openSX70/openSX70-PCB/CURRENT/openSX70_LENS&BELLOWS_V5.1-SEEED_20180224-blue.png

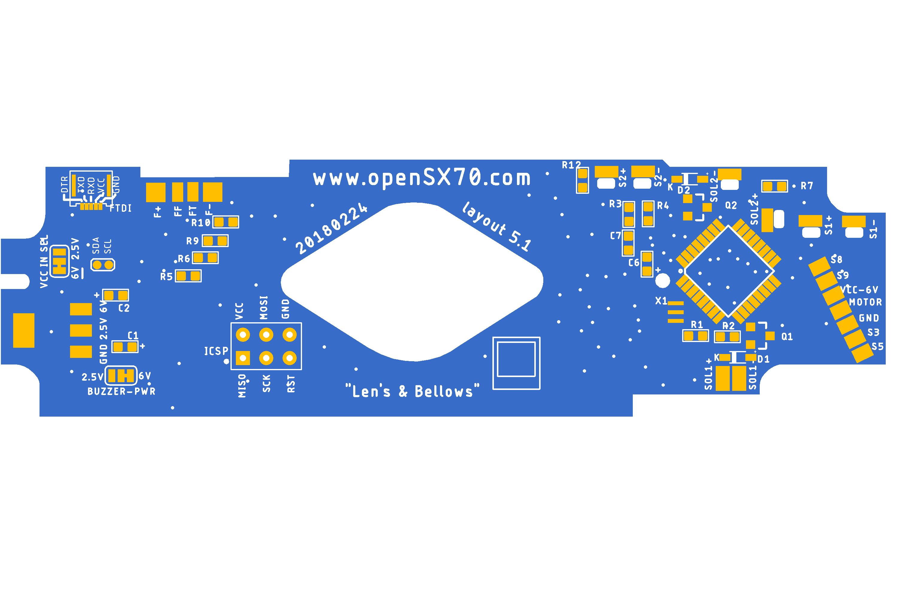
CURRENT/openSX70_LENS&BELLOWS_V5.1-SEEED_20180224-blue.png
