openSX70/openSX70-PCB/CURRENT/sonar-FBW/openSX70_SONAR_8-9-3-8-S4-TCS3200-202000606.xlsx

Sheet: openSX70-sonar-PCBWAY BOM
 |  |  | BOM
Item # | *Ref Des | *Qty | Manufacturer | *Mfg Part # | Description / Value | *Package | Type | Your Instructions / Notes
1 | C1, C4 | 2 | any/open AVL | 10uF | CERAMIC-10UF-10V-10%-X5R(0603) | C0603 | SMD | any brand-name manufacturer from AVL
2 | C2, C3, C5, C6, C7, C8, C9 | 7 | any/open AVL | 100nF | CERAMIC-100NF-50V-10%-X7R(0603) | C0603 | SMD | any brand-name manufacturer from AVL
3 | R2, R4, R16 | 3 | any/open AVL | 100K | SMD-RES-100K-5%-1/10W(0603) | R0603 | SMD | any brand-name manufacturer from AVL
4 | R1, R3, R7, R23 | 4 | any/open AVL | 100R | SMD-RES-100R-5%-1/10W(0603) | R0603 | SMD | any brand-name manufacturer from AVL
5 | R5, R8, R12, R14, R9, R24 | 6 | any/open AVL | 10K | SMD-RES-10K-1%-1/10W(0603) | R0603 | SMD | any brand-name manufacturer from AVL
6 | R6, R10, R13, R15, R25 | 6 | any/open AVL | 12K | SMD-RES-12K-1%-1/10W(0603) | R0603 | SMD | any brand-name manufacturer from AVL
7 | R11, R18, R20, R22 | 4 | any/open AVL | 1K 1/10W | SMD-RES-1K-5%-1/10W(0603) | R0603 | SMD | any brand-name manufacturer from AVL
8 | R19 | 1 | any/open AVL | 150R 1/10W | SMD-RES-150R-5%-1/10W(0603) | R0603 | SMD | any brand-name manufacturer from AVL
9 | R21 | 1 | any/open AVL | 180R 1/10W | SMD-RES-180R-5%-1/10W(0603) | R0603 | SMD | any brand-name manufacturer from AVL
10 | R17 | 1 | any/open AVL | 120K 1/10W | SMD-RES-120K-5%-1/10W(0603) | R0603 | SMD | any brand-name manufacturer from AVL
11 | D1, D2 | 2 | any/open AVL | 1N4148WS | 1N4148WS Series 75 V 300 mA Surface Mount Small Signal Diodes | SOD323 | SMD | Polarity marked
12 | Q1, Q2 | 2 | Alpha Omega | MOSFET-NCH-AO3404A | 5.8A/30V/35mΩ | SOT23-3 | SMD | DO NOT REPLACE MUST USE THIS
13 | J1 | 1 | Wurth Electronics | 687106183722 | WR-FPC SMT Horiztl .50mm Bott Cont 6P | 687106183722 | SMD
14 | U1 | 1 | Microchip Technology | ATMEGA328P-MU | ATMEGA328P_32MLF | MLF32 | SMD | no thermal pad implemented there are NO vias under
15 | U2 | 1 | Texas Instruments | TPS79533DCQR | Ultralow-Noise, High-PSRR, Fast, RF, 500-mA Low-Dropout Linear Regulators 6-SOT-223 -40 to 125 | SOT-223-6 | SMD | 3.3V operation
16 | X1 | 1 | Murata Electronics North America | CSTNE8M00G550000R0 | Resonators 8.0000MHz 33pF SMD | CFP95P160X100-3N | SMD | Resonators 8MHz 5%
17 | LED | 1 | Lite-On Inc. | LTST-C195TBJRKT | Blue/Red Clear | 0606 | SMD
18 | U3 | 1 | AMS | TCS3200D-TR | Light To Frequency & Light To Voltage Light to Frequency High Responsivity | SOIC8 | SMD
19 | Q3 |  | any/open AVL | BC8743 | NPN transistor | SOT-23 | SMD
20 | Q4 |  | Diodes Incorporated | DMP2035U-7 | MOSFET MOSFET P-CHANNEL | SOT-23 | SMD
 |  | 45
 |  |  | AVL (Approved Vendor List)
 |  |  | TDK, Murata, Taiyo Yuden, AVX, Panasonic, Samsung, Vishay, ON Semiconductor, Diodes Incorporated

Sheet: openSX70_SONAR_8-8-S4-TCS3200-2
item# | ref desp | Qty | manufacturer | Value | Device | Package | type | Description
1 | C1, C4 | 2 | various | 10uF | CERAMIC-10UF-10V-10%-X5R(0603) | C0603 | SMD | 302010103
2 | C2, C3, C5, C6, C7, C8, C9 | 7 | various | 100nF | CERAMIC-100NF-50V-10%-X7R(0603) | C0603 | SMD | 302010138
3 | R2, R4 | 2 | various | 100K | SMD-RES-100K-5%-1/10W(0603) | R0603 | SMD | 301010089
4 | R1, R3, R7 | 3 | various | 100R | SMD-RES-100R-5%-1/10W(0603) | R0603 | SMD | 301010090
5 | R8, R12, R14, R16, R5, R9 | 6 | various | 10K | SMD-RES-10K-1%-1/10W(0603) | R0603 | SMD | 301010299
6 | R6, R10, R13, R15, R17 | 5 | various | 12K | SMD-RES-12K-1%-1/10W(0603) | R0603 | SMD | 301010299
7 | R11, R18 | 2 | various | 1K 1/10W | SMD-RES-1K-5%-1/10W(0603) | R0603 | SMD | 301010291
8 | D1, D2 | 2 | various | 1N4148WS | Small Signal Fast Switching Diode | SOD323 | SMD | 1N4148WS Series 75 V 300 mA Surface Mount Small Signal Diodes - SOD-323F
9 | Q1, Q2 | 2 | Alpha Omega | 5.8A/30V/35mΩ | MOSFET-NCH-AO3404A | SOT23-3 | SMD | N-channel MOSFETs
10 | J1 | 1 | Wurth Electronics | 687106183722 | WR-FPC SMT Horiztl .50mm Bott Cont 6P | 687106183722 | SMD
11 | U1 | 1 | ATMEL | ATMEGA328P_32MLF | ATMEGA328P_32MLFATMEGA328-MLF | MLF32 | SMD
12 | U2 | 1 | Texas Instruments | TPS79533DCQR | TPS79501DCQ | SOT-223-6 | SMD | Ultralow-Noise, High-PSRR, Fast, RF, 500-mA Low-Dropout Linear Regulators 6-SOT-223 -40 to 125
13 | Y1 | 1 | MURATA | CSTCE8M00G52Z-R0 | CER RES 16.0000MHZ 15PF SMD | CFP95P160X100-3N | SMD | Ceramic Resonator 16MHz ±0.5% (Tol) ±0.3% (Stability) 15pF 40Ohm 3-Pin CSMD T/R
14 | LED | 1 | Lite-On Inc. | LTST-C195KGJRKT | BI-LED RED GREEN | 0606 | SMD
15 | TCS3200 | 1 | TAOS | TCS3200D | TCS3200D | SOIC8 | SMD

Sheet: PCBWAY example
 |  |  | BOM
Item # | *Ref Des | *Qty | Manufacturer | *Mfg Part # | Description / Value | *Package | Type | Your Instructions / Notes
1 | U2 | 1 | STMicroelectronics | LIS3MDLTR | SENSOR MAGMTR I2C/SPI 12LGA | 12LGA | SMD | Align dot on chip with dot on PCB (pin 1)
2 | U1 | 1 | STMicroelectronics | LSM6DS33TR | IMU ACCEL/GYRO I2C/SPI 16LGA | 16LGA | SMD | Align dot on chip with dot on PCB (pin 1)
3 | C1,C2,C3,C4 | 4 | Yageo | CC0603KRX7R7BB104 | CAP CER 0.1UF 16V X7R 0603 | 0603 | SMD
4 | C5 | 1 | Murata Electronics North America | GRM188R61C105MA12D | CAP CER 1UF 16V X5R 0603 | 0603 | SMD
5 | J1 | 1 | JST Sales America Inc. | SM09B-SRSS-TB(LF)(SN) | CONN HEADER SH 9POS SIDE 1MM TIN | 9POS | SMD
