openSX70/openSX70-PCB/CURRENT/GERBERS/openSX70_LENS&BELLOWS_V5.2-SEEED_20180226_NO_BUZZER.csv

Designator | Manufacturer Part Number | Quantity
LED1 | 17-215UYC/S530-A3/TR8 | 1
C7, C2, C6 | CC0603KRX7R9BB104 | 3
R2, R4 | RC0603FR-07100KL | 2
R1, R3, R7 | RC0603JR-07100RL | 3
R6, R10, R12 | RC0603FR-0710KL | 3
C1, C5 | CC0603KRX5R6BB106 | 2
R5, R9 | RC0603FR-0715KL | 2
R8, R13 | RC0603FR-071KL | 2
D1,D2 | 1N4148WS | 2
R14 | RC0603JR-074K7L | 1
Q1, Q2 | AO3404A | 2
U1 | ATMEGA328P-AU | 1
U3 | BH1750FVI-TR | 1
Y1 | CSTCE8M00G52Z-R0 | 1
J1 | 687106183722 | 1
LD11172.5V | LD1117S25CTR | 1
