openSX70/openSX70-PCB/CURRENT/openSX70_ALPHA_V8-20181105-MLF32.brd

## EAGLE design CURRENT/openSX70_ALPHA_V8-20181105-MLF32.brd (2018-11-05)

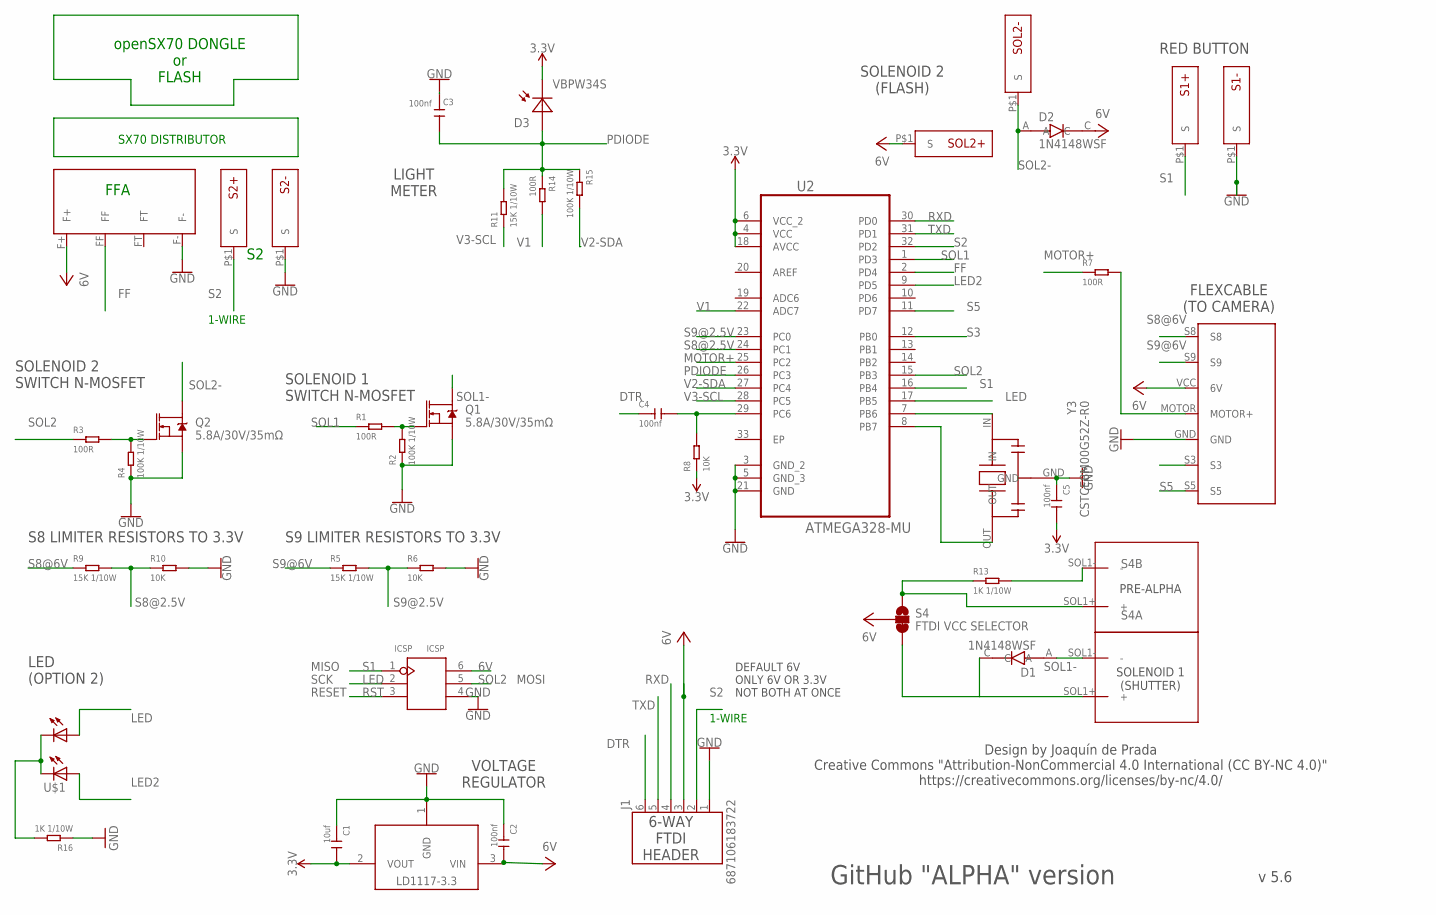
[picture p19: schematic openSX70_ALPHA_V8-20181105-MLF32.sch]

Parts:
C1: 10uf; C0603
C2, C3, C4, C5: 100nf; C0603
D1, D2: 1N4148WSF; SODFL2512X100N
D3: VBPW34S; SOD6439X130N
ICSP: ICSP; H2X3-2.54
J1: 687106183722
LD11172.5V: LD1117 2.5V; SOT223
Q1, Q2: 5.8A/30V/35mΩ; SOT23-3
R1, R3, R7, R14: 100R; R0603
R2, R4, R15: 100K 1/10W; R0603
R5, R9, R11: 15K 1/10W; R0603
R6, R8, R10: 10K; R0603
R13, R16: 1K 1/10W; R0603
S1+, S1-, S2+, S2-: SX70-S-PAD-NEW; SX70-S-PAD2
S4: FTDI VCC SELECTOR; SMT-JUMPER_3_1-NC_TRACE_SILK
SOL1, SOL2: SX70-SOLENOID1-2PADS; SX70-SOLENOID1-2
SOL2+, SOL2-: SX70-S-PAD-NEW; SX70-S-PAD2
U2: ATMEGA328-MU; QFN50P500X500X100-33N
U$1: DUAL-LED-0603-BIS; LED_APHB1608SYKSURKC
U$2: FFA; FFA-PAD-PACKAGE
U$3: SX70-7-PAD; SX70-7-PAD-PROPER
Y3: CSTCE8M00G52Z-R0; CFP95P160X100-3N

Connections:
3.3V: C1.2, C5.2, D3.C, LD11172.5V.2 (VOUT), R8.1, U2.4 (VCC), U2.6 (VCC_2), U2.18 (AVCC)
6V: C2.2, D2.C, ICSP.6 (VCC), J1.3 (4), LD11172.5V.3 (VIN), S4.2, SOL2+.P$1, U$2.F+, U$3.VCC (6V)
DTR: C4.1, J1.6 (1)
FF: U2.2 (PD4), U$2.FF
GND: C1.1, C2.1, C3.2, C5.1, ICSP.4 (GND), J1.1 (6), LD11172.5V.1 (GND), Q1.2 (S), Q2.2 (S), R2.1, R4.1, R6.2, R10.2, R16.1, S1-.P$1, S2-.P$1, U2.3 (GND_2), U2.5 (GND_3), U2.21 (GND), U$2.F-, U$3.GND, Y3.GND
LED: ICSP.2 (SCK), U2.17 (PB5), U$1.1 (A)
LED2: U2.9 (PD5), U$1.3 (A1)
MOTOR+: R7.1, U2.25 (PC2)
MOTOR-HEADER: R7.2, U$3.MOTOR (MOTOR+)
unnamed: Q1.1 (G), R1.2, R2.2
unnamed: D1.C, S4.3, SOL1.SOL1+ (+)
unnamed: Q2.1 (G), R3.2, R4.2
unnamed: U2.7 (PB6), Y3.IN
unnamed: R16.2, U$1.2 (C), U$1.4 (C1)
unnamed: R13.2, SOL2.SOL1- (-)
unnamed: R13.1, S4.1, SOL2.SOL1+ (+)
unnamed: U2.8 (PB7), Y3.OUT
unnamed: C4.2, R8.2, U2.29 (PC6)
PDIODE: C3.1, D3.A, R11.2, R14.1, R15.1, U2.26 (PC3)
RST: ICSP.3 (RST)
RXD: J1.4 (3), U2.30 (PD0)
S1: ICSP.1 (MISO), S1+.P$1, U2.16 (PB4)
S2: J1.2 (5), S2+.P$1, U2.32 (PD2)
S3: U2.12 (PB0), U$3.S3
S5: U2.11 (PD7), U$3.S5
S8@2.5V: R9.2, R10.1, U2.24 (PC1)
S8@6V: R9.1, U$3.S8
S9@2.5V: R5.2, R6.1, U2.23 (PC0)
S9@6V: R5.1, U$3.S9
SOL1: R1.1, U2.1 (PD3)
SOL1-: D1.A, Q1.3 (D), SOL1.SOL1- (-)
SOL2: ICSP.5 (MOSI), R3.1, U2.15 (PB3)
SOL2-: D2.A, Q2.3 (D), SOL2-.P$1
TXD: J1.5 (2), U2.31 (PD1)
V1: R14.2, U2.22 (ADC7)
V2-SDA: R15.2, U2.27 (PC4)
V3-SCL: R11.1, U2.28 (PC5)

Notes on the sheet:
1-WIRE
FFA
LIGHT METER
FLEXCABLE (TO CAMERA)
RED BUTTON
SOLENOID 1 (SHUTTER)
SOLENOID 2 (FLASH)
6-WAY FTDI HEADER
VOLTAGE REGULATOR
S8 LIMITER RESISTORS TO 3.3V
S9 LIMITER RESISTORS TO 3.3V
SOLENOID 2 SWITCH N-MOSFET
SOLENOID 1 SWITCH N-MOSFET
SX70 DISTRIBUTOR
openSX70 DONGLE or FLASH
v 5.6
Design by Joaquín de Prada Creative Commons "Attribution-NonCommercial 4.0 International (CC BY-NC 4.0)" https://creativecommons.org/licenses/by-nc/4.0/
GitHub "ALPHA" version
DEFAULT 6V ONLY 6V OR 3.3V NOT BOTH AT ONCE
MISO
SCK
RESET
MOSI
S4A
S4B
PRE-ALPHA
LED (OPTION 2)

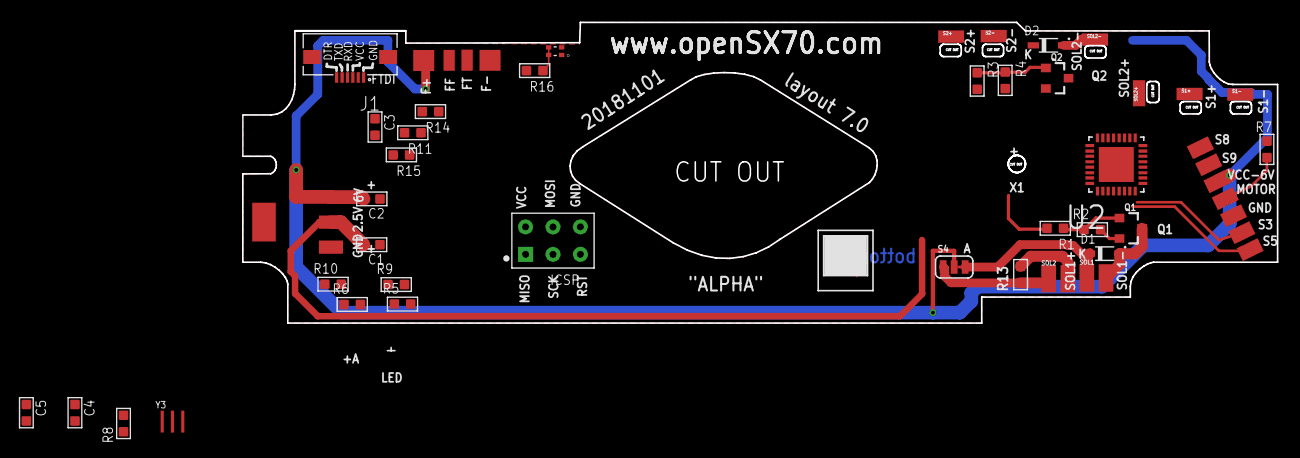
[picture p20: board openSX70_ALPHA_V8-20181105-MLF32.brd from above]

Board: 2 copper layers, 95.9 x 27.9 mm, 42 parts (1 on the bottom side), 36 nets.
