openSX70/openSX70-PCB/CURRENT/simblee/SparkFun_Simblee_Breakout_v11.brd

## EAGLE design CURRENT/simblee/SparkFun_Simblee_Breakout_v11.brd (2018-11-05)

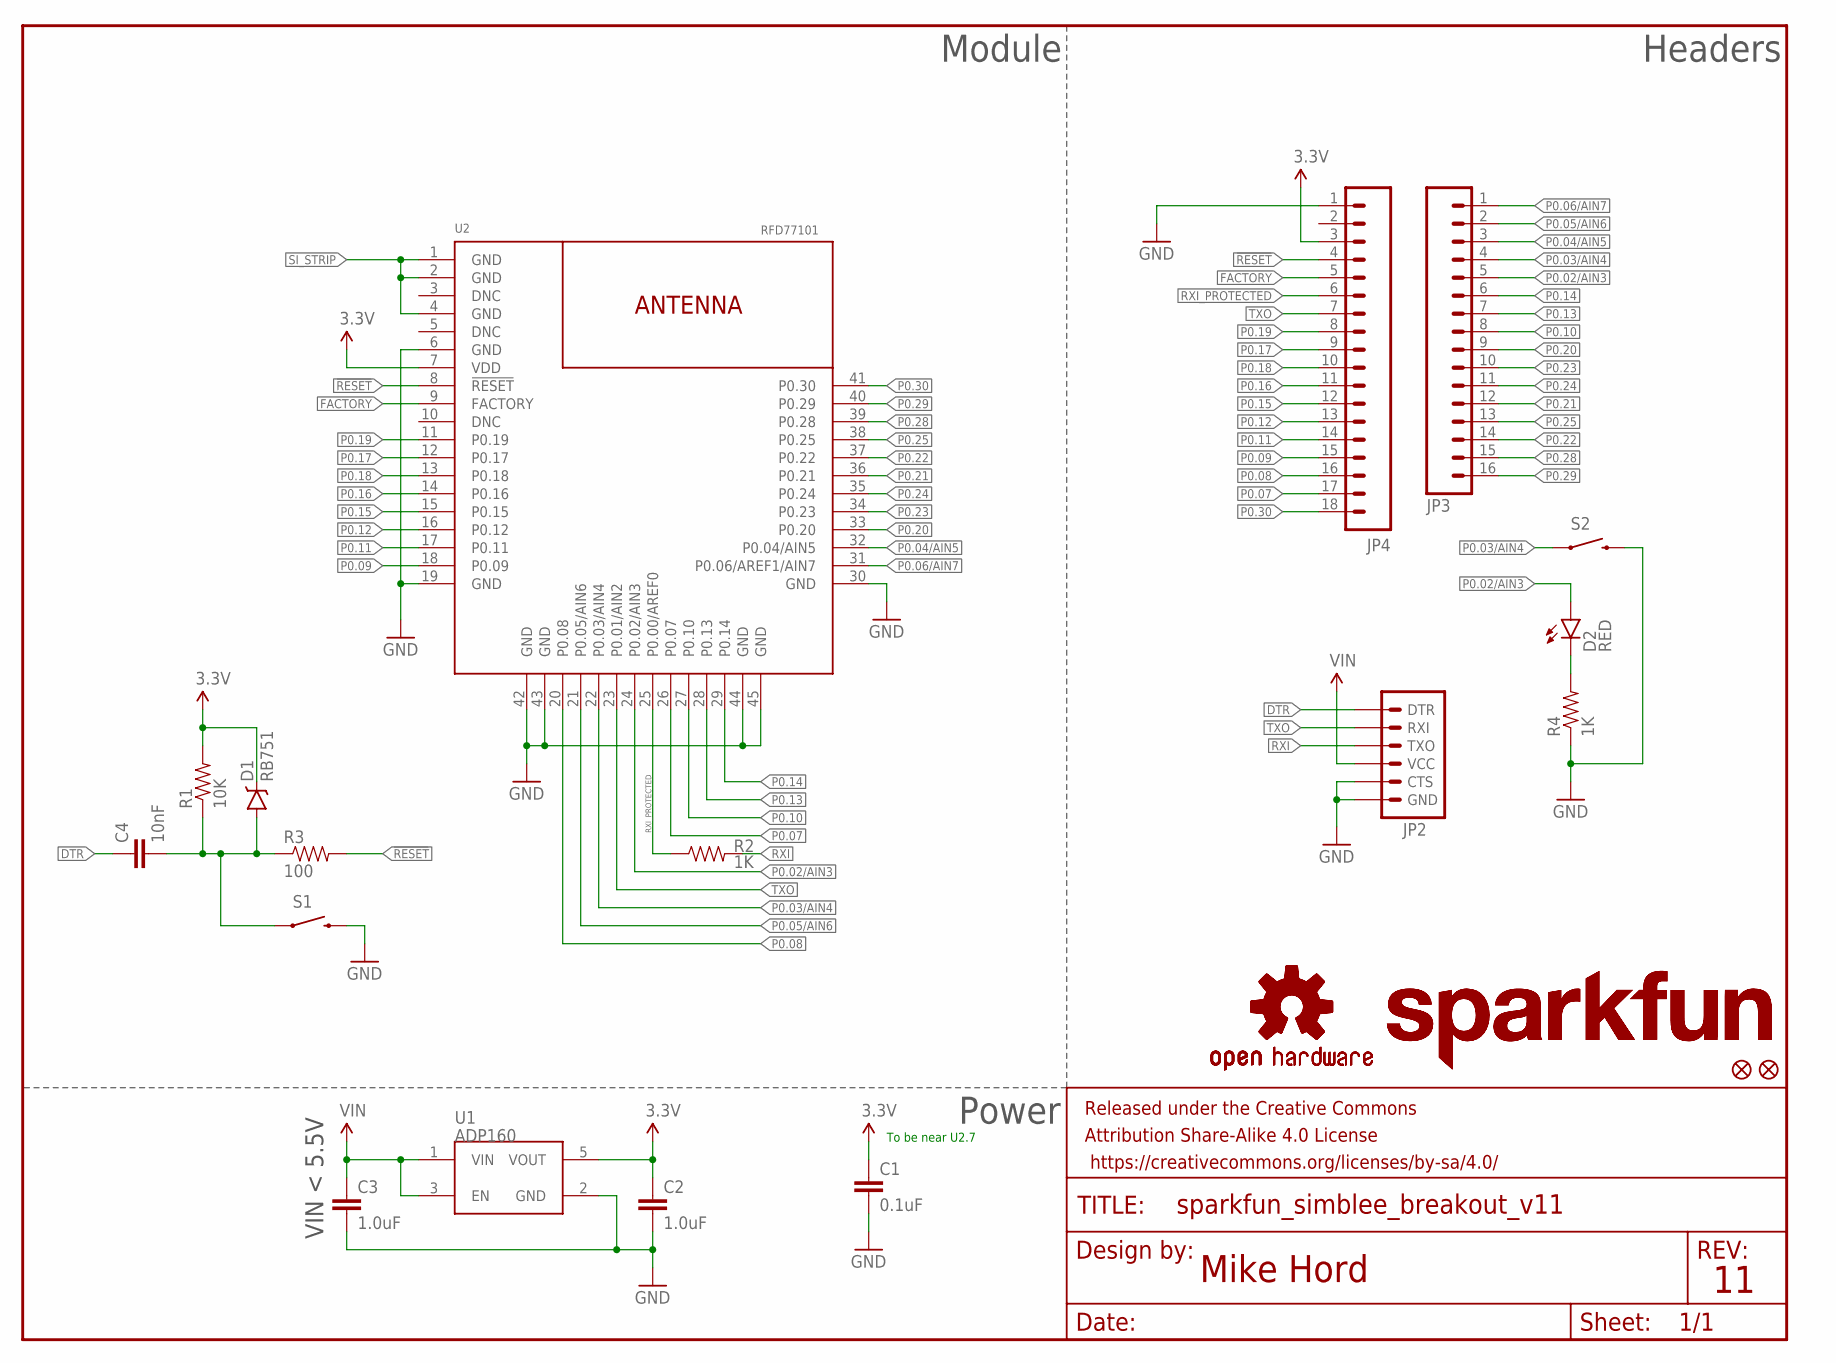
[picture p21: schematic SparkFun_Simblee_Breakout_v11.sch]

Parts:
C1: 0.1uF; 0603-CAP
C2, C3: 1.0uF; 0603-CAP
C4: 10nF; 0603-CAP
D1: RB751; SOD-523
D2: RED; LED-0603
FID1, FID2: FIDUCIALUFIDUCIAL; MICRO-FIDUCIAL
FRAME1: FRAME-LETTER; CREATIVE_COMMONS
JP2: ARDUINO_SERIAL_PROGRAMPTH; 1X06
JP3: M16PTH; 1X16
JP4: M18_; 1X18
LOGO1, LOGO3: SFE_LOGO_NAME.1_INCH; SFE_LOGO_NAME_.1
LOGO2, LOGO4: OSHW-LOGOS; OSHW-LOGO-S
R1: 10K; 0603-RES
R2, R4: 1K; 0603-RES
R3: 100; 0603-RES
S1, S2: SWITCH-MOMENTARY-2SMD; TACTILE-SWITCH-SMD
U1: ADP160; SOT23-5
U2: RFD77101

Connections:
3.3V: C1.1, C2.1, D1.C, JP4.3, R1.2, U1.5 (VOUT), U2.7 (VDD)
!RESET: JP4.4, R3.2, U2.8 (!RESET!)
DTR: C4.1, JP2.1 (DTR)
FACTORY: JP4.5, U2.9 (FACTORY)
GND: C1.2, C2.2, C3.2, JP2.5 (CTS), JP2.6 (GND), JP4.1, R4.1, S1.3 (2), S2.3 (2), U1.2 (GND), U2.6 (GND), U2.19 (GND), U2.30 (GND), U2.42 (GND), U2.43 (GND), U2.44 (GND), U2.45 (GND)
unnamed: C4.2, D1.A, R1.1, R3.1, S1.1
unnamed: D2.C, R4.2
P0.02/AIN3: D2.A, JP3.5, U2.24 (P0.02/AIN3)
P0.03/AIN4: JP3.4, S2.1, U2.22 (P0.03/AIN4)
P0.04/AIN5: JP3.3, U2.32 (P0.04/AIN5)
P0.05/AIN6: JP3.2, U2.21 (P0.05/AIN6)
P0.06/AIN7: JP3.1, U2.31 (P0.06/AREF1/AIN7)
P0.07: JP4.17, U2.26 (P0.07)
P0.08: JP4.16, U2.20 (P0.08)
P0.09: JP4.15, U2.18 (P0.09)
P0.10: JP3.8, U2.27 (P0.10)
P0.11: JP4.14, U2.17 (P0.11)
P0.12: JP4.13, U2.16 (P0.12)
P0.13: JP3.7, U2.28 (P0.13)
P0.14: JP3.6, U2.29 (P0.14)
P0.15: JP4.12, U2.15 (P0.15)
P0.16: JP4.11, U2.14 (P0.16)
P0.17: JP4.9, U2.12 (P0.17)
P0.18: JP4.10, U2.13 (P0.18)
P0.19: JP4.8, U2.11 (P0.19)
P0.20: JP3.9, U2.33 (P0.20)
P0.21: JP3.12, U2.36 (P0.21)
P0.22: JP3.14, U2.37 (P0.22)
P0.23: JP3.10, U2.34 (P0.23)
P0.24: JP3.11, U2.35 (P0.24)
P0.25: JP3.13, U2.38 (P0.25)
P0.28: JP3.15, U2.39 (P0.28)
P0.29: JP3.16, U2.40 (P0.29)
P0.30: JP4.18, U2.41 (P0.30)
RXI: JP2.3 (TXO), R2.2
RXI_PROTECTED: JP4.6, R2.1, U2.25 (P0.00/AREF0)
SI_STRIP: U2.1 (GND), U2.2 (GND), U2.4 (GND)
TXO: JP2.2 (RXI), JP4.7, U2.23 (P0.01/AIN2)
VIN: C3.1, JP2.4 (VCC), U1.1 (VIN), U1.3 (EN)

Notes on the sheet:
Mike Hord
VIN < 5.5V
Module
Power
Headers
To be near U2.7

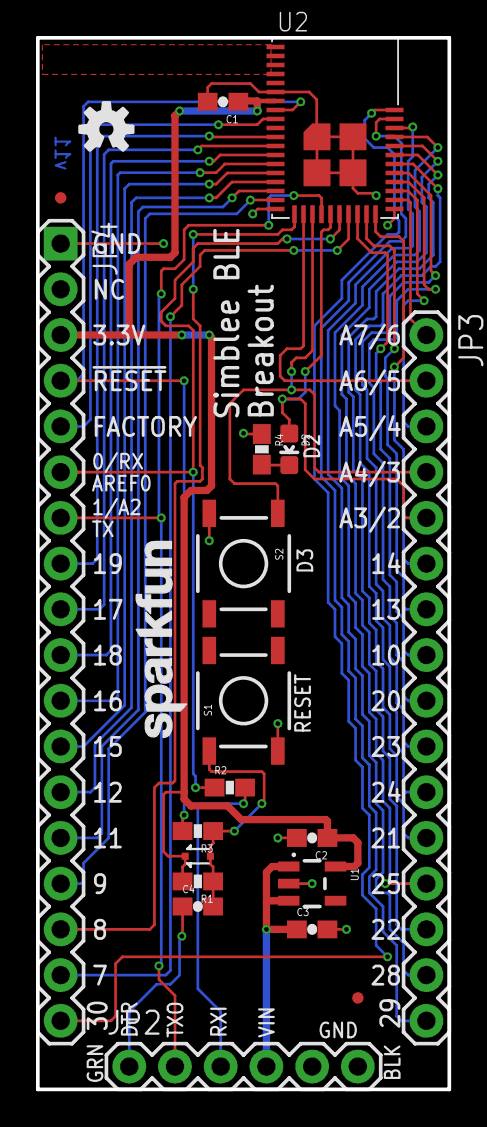
[picture p22: board SparkFun_Simblee_Breakout_v11.brd from above]

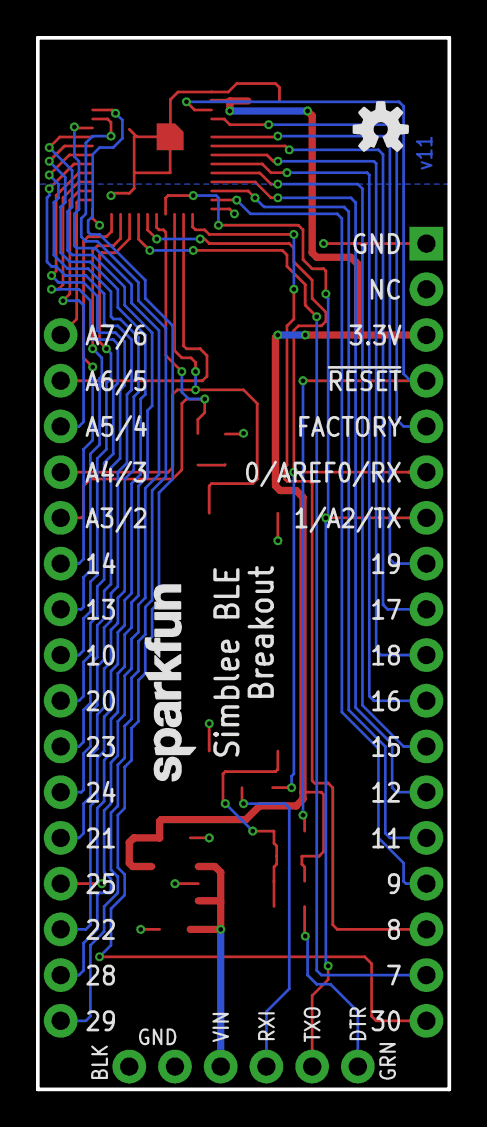
[picture p23: board SparkFun_Simblee_Breakout_v11.brd from below]

Board: 2 copper layers, 22.9 x 58.4 mm, 24 parts (2 on the bottom side), 39 nets.
